hotkeysoft/wizardElectronicGame-kicad/src/WizardGame/rom.h

const uint8_t masterMerlinRom[] PROGMEM = {
	0x2C, 0x4F, 0x61, 0x7F, 0x45, 0x27, 0x0A, 0x0E, 0x92, 0x7C, 0x9F, 0x85, 0x2C, 0x41, 0x60, 0x4F, 
	0x32, 0x83, 0x08, 0x79, 0x96, 0x72, 0x06, 0x25, 0x3B, 0xA4, 0x43, 0x3E, 0xB9, 0x27, 0xA4, 0x43, 
	0x07, 0x9D, 0x4D, 0x37, 0x40, 0x21, 0x05, 0x06, 0x46, 0x03, 0x04, 0xA9, 0x18, 0x39, 0xB3, 0x4E, 
	0x3E, 0x80, 0x10, 0x27, 0x83, 0x4F, 0x2C, 0x62, 0xA4, 0x45, 0x21, 0x4F, 0x18, 0x3B, 0xB0, 0x8E, 
	0x60, 0x3E, 0x71, 0x92, 0x76, 0x27, 0x28, 0x45, 0x3B, 0x90, 0x0C, 0x04, 0x88, 0x2C, 0x10, 0x83, 
	0x0D, 0x8B, 0x27, 0x4F, 0x38, 0xAB, 0x71, 0x30, 0x28, 0x40, 0x3F, 0xA1, 0x05, 0x5D, 0x9A, 0x45, 
	0x69, 0x45, 0x38, 0xAE, 0x04, 0xA2, 0x2C, 0x4F, 0x3A, 0xB0, 0x8E, 0x70, 0x34, 0x98, 0x27, 0xA4, 
	0x4D, 0x33, 0xB8, 0x46, 0x3F, 0xBE, 0x3E, 0x75, 0x10, 0x4F, 0x36, 0x35, 0x37, 0x0F, 0x21, 0xB8, 
	0x41, 0x61, 0xF3, 0x4A, 0xE9, 0x41, 0xF4, 0x4E, 0xEF, 0x44, 0xE9, 0x49, 0xF4, 0x42, 0xEF, 0x40, 
	0x61, 0xEB, 0x45, 0xF4, 0x1A, 0xC0, 0x0F, 0x1F, 0xED, 0x61, 0x45, 0xF4, 0x44, 0x61, 0x49, 0xF4, 
	0x48, 0x1C, 0xF7, 0x41, 0xF4, 0x48, 0xEF, 0x1C, 0x80, 0x61, 0x05, 0x61, 0x61, 0x61, 0x0F, 0x60, 
	0x05, 0x60, 0x0F, 0x4E, 0x23, 0x13, 0xC2, 0x17, 0xC0, 0x2C, 0x4F, 0x31, 0x18, 0xC6, 0x28, 0x0F, 
	0xF7, 0x14, 0xF3, 0x42, 0x14, 0xEF, 0xF7, 0x45, 0x61, 0x46, 0x14, 0xF4, 0x1A, 0xC0, 0x0F, 0x48, 
	0x2C, 0x21, 0x2E, 0x27, 0x76, 0x93, 0x04, 0x90, 0x12, 0x80, 0x1F, 0xC0, 0x2A, 0x42, 0x69, 0x69, 
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
	0xA5, 0x0B, 0x15, 0xC0, 0x0B, 0x0B, 0x3A, 0x80, 0x0B, 0x4C, 0x21, 0x41, 0x06, 0x24, 0x3E, 0x27, 
	0x15, 0xB7, 0x28, 0x20, 0x3F, 0xB7, 0xB8, 0x40, 0x2D, 0x0F, 0x0B, 0x17, 0xF1, 0x1E, 0x80, 0x00, 
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
	};
